Szymon423/Numpad/Hardware/3D_Model/Renders/00.png

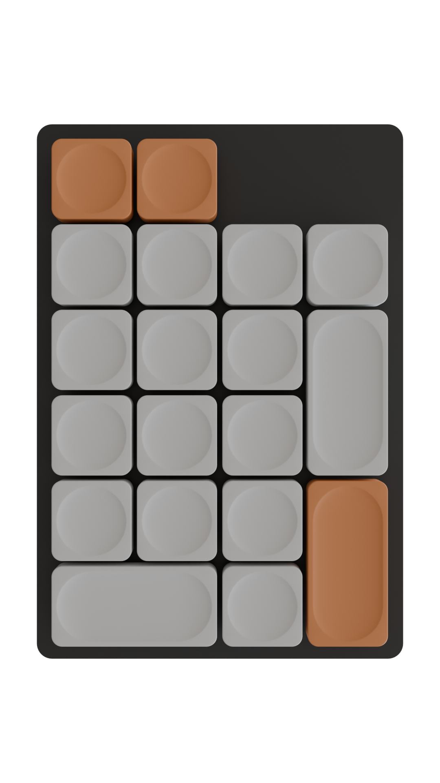
Hardware/3D_Model/Renders/00.png
