Szymon423/Numpad/Hardware/3D_Model/Renders/06.png

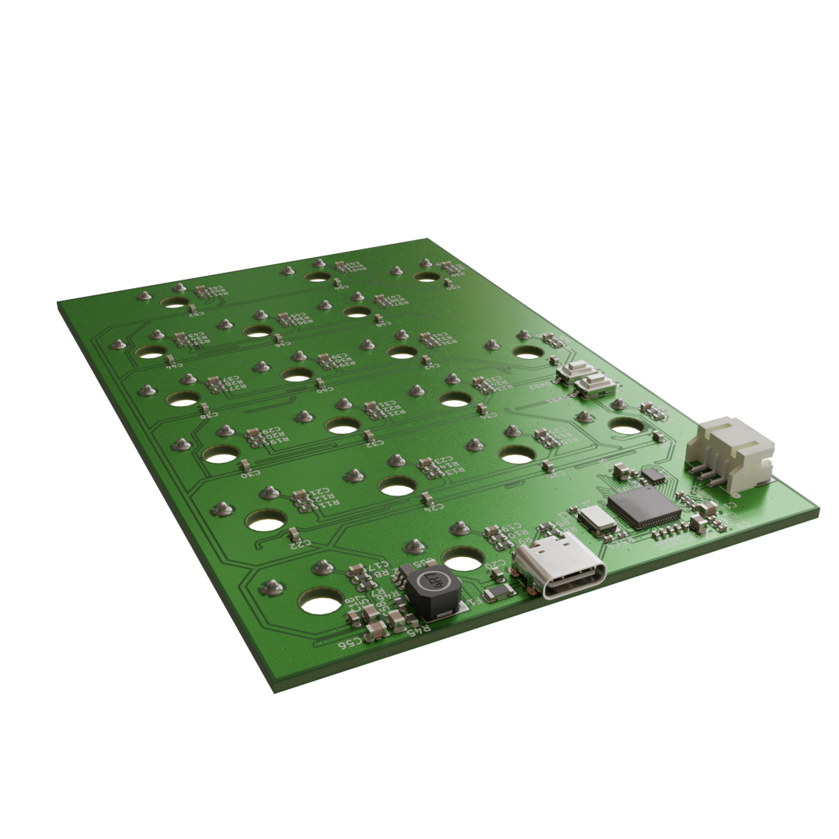
Hardware/3D_Model/Renders/06.png
