Szymon423/Numpad/Software/src/definitions.hpp

#pragma once
#include "pico/stdlib.h"

namespace Constants {
    constexpr uint8_t PixelPin{ 21 };
    constexpr uint8_t PixelNumber{ 19 };
    constexpr uint8_t ButtonNumber{ 19 };

    constexpr uint8_t Button0Pin{ 14 };
    constexpr uint8_t Button1Pin{ 15 };
    constexpr uint8_t Button2Pin{ 13 };
    constexpr uint8_t Button3Pin{ 6 };
    constexpr uint8_t Button4Pin{ 16 };
    constexpr uint8_t Button5Pin{ 12 };
    constexpr uint8_t Button6Pin{ 7 };
    constexpr uint8_t Button7Pin{ 17 };
    constexpr uint8_t Button8Pin{ 11 };
    constexpr uint8_t Button9Pin{ 8 };
    constexpr uint8_t ButtonPlusPin{ 3 };
    constexpr uint8_t ButtonMinusPin{ 2 };
    constexpr uint8_t ButtonDividePin{ 10 };
    constexpr uint8_t ButtonMultiplyPin{ 9 };
    constexpr uint8_t ButtonDotPin{ 5 };
    constexpr uint8_t ButtonEnterPin{ 4 };
    constexpr uint8_t ButtonNumlocPin{ 18 };
    constexpr uint8_t ButtonMicPin{ 20 };
    constexpr uint8_t ButtonLEDPin{ 19 };
}  
